Dieu-de-l-elec/Custom-Segmented-Display/CAD and RENDERS/PCB Routing PART4 3.png

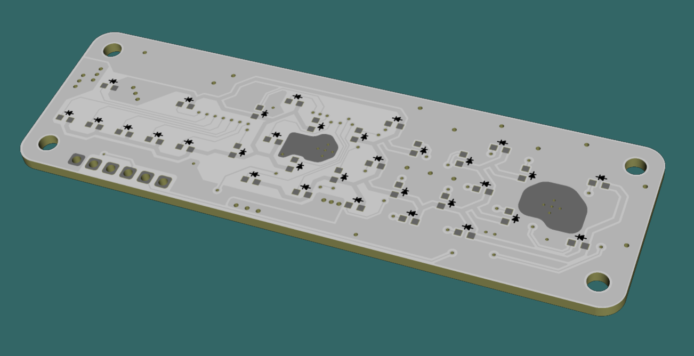
CAD and RENDERS/PCB Routing PART4 3.png
