Dieu-de-l-elec/Custom-Segmented-Display/CAD and RENDERS/PCB Routing PART4 4.png

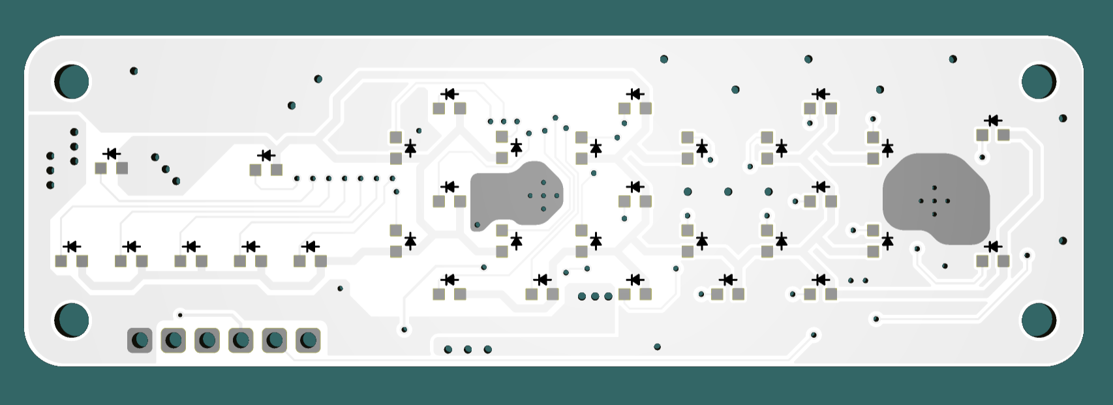
CAD and RENDERS/PCB Routing PART4 4.png
