Dieu-de-l-elec/Custom-Segmented-Display/CAD and RENDERS/PCB Routing PART4 6.png

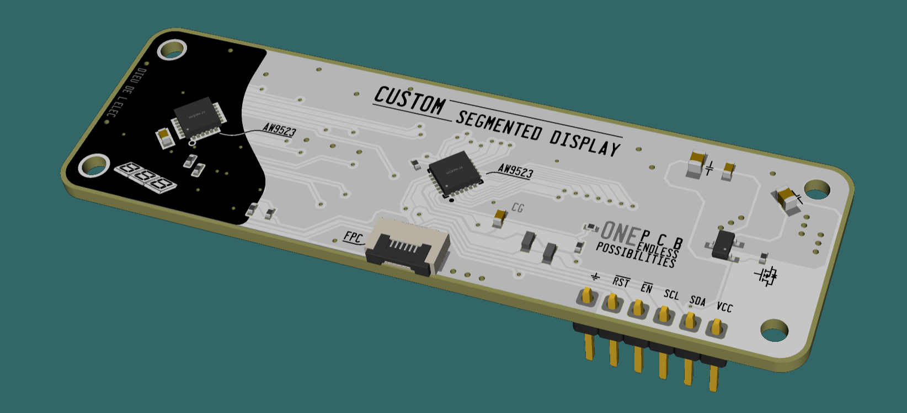
CAD and RENDERS/PCB Routing PART4 6.png
