Dieu-de-l-elec/Custom-Segmented-Display/CAD and RENDERS/RENDER 1.png

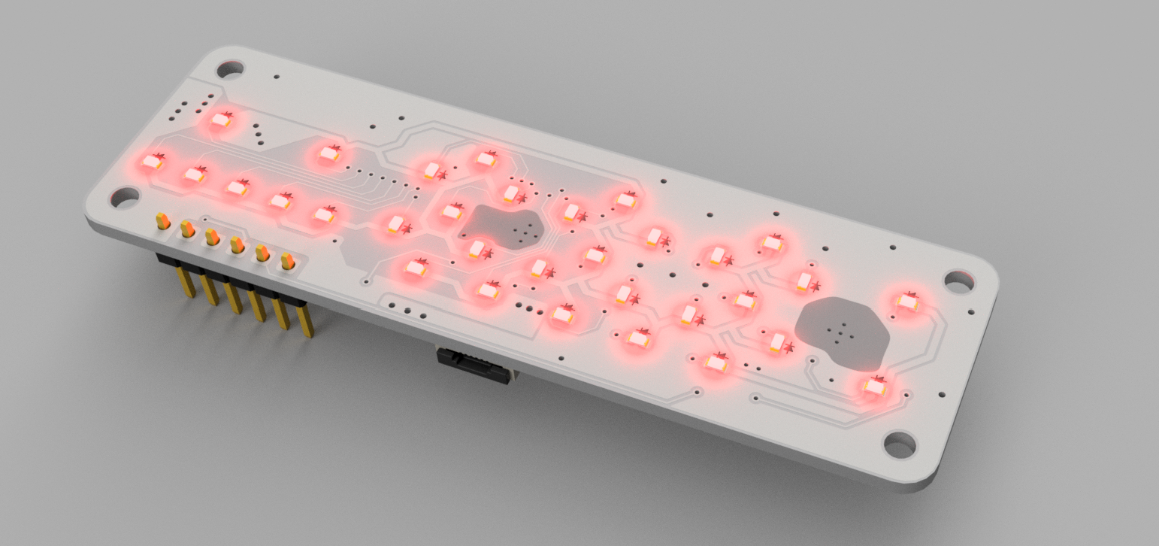
CAD and RENDERS/RENDER 1.png
