Dieu-de-l-elec/Custom-Segmented-Display/CAD and RENDERS/RENDER 1B.png

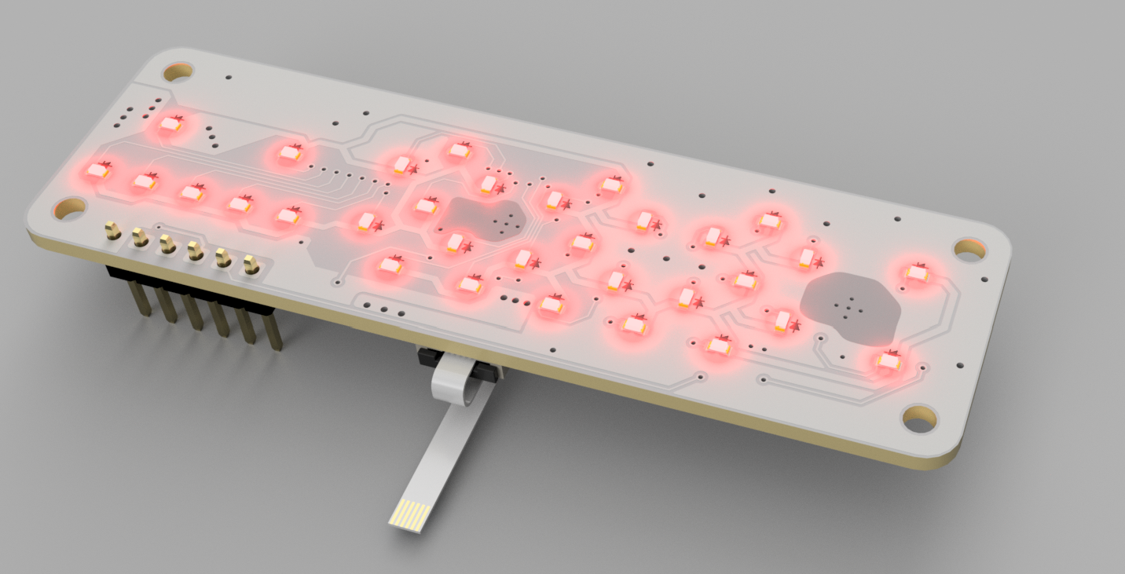
CAD and RENDERS/RENDER 1B.png
