Dieu-de-l-elec/Custom-Segmented-Display/CAD and RENDERS/RENDER 2.png

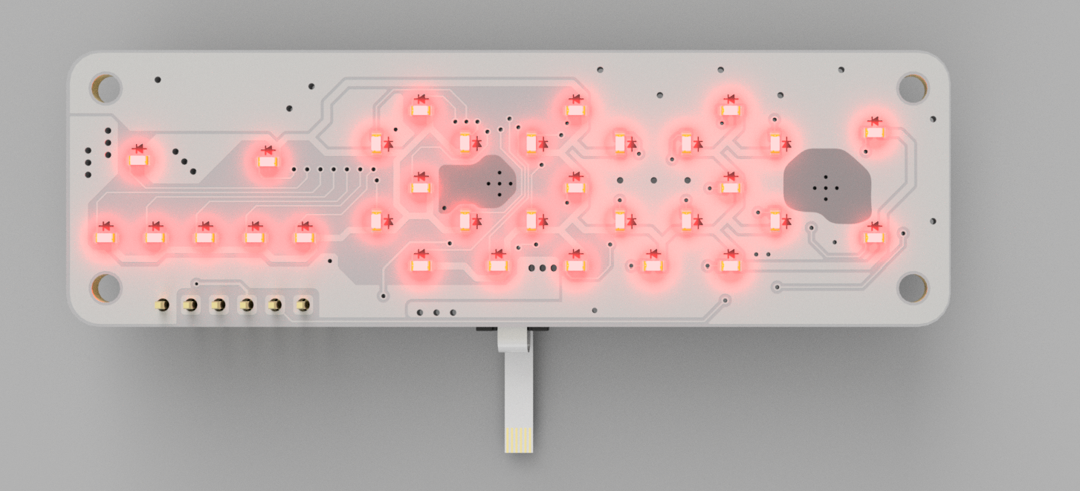
CAD and RENDERS/RENDER 2.png
