Dieu-de-l-elec/Custom-Segmented-Display/CAD and RENDERS/RENDER 3.png

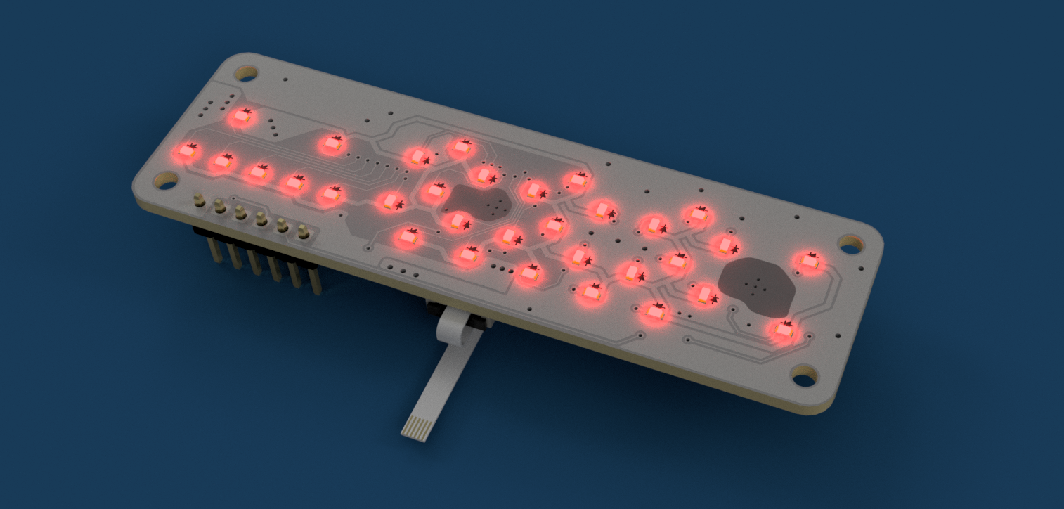
CAD and RENDERS/RENDER 3.png
