Dieu-de-l-elec/Custom-Segmented-Display/CAD and RENDERS/RENDER 4.png

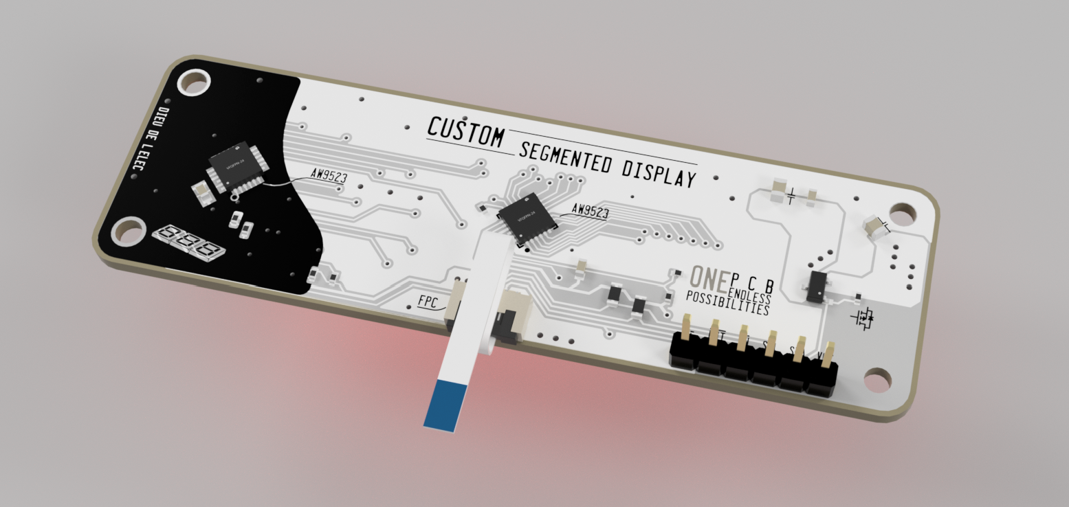
CAD and RENDERS/RENDER 4.png
