Dieu-de-l-elec/Custom-Segmented-Display/CAD and RENDERS/RENDER 5.png

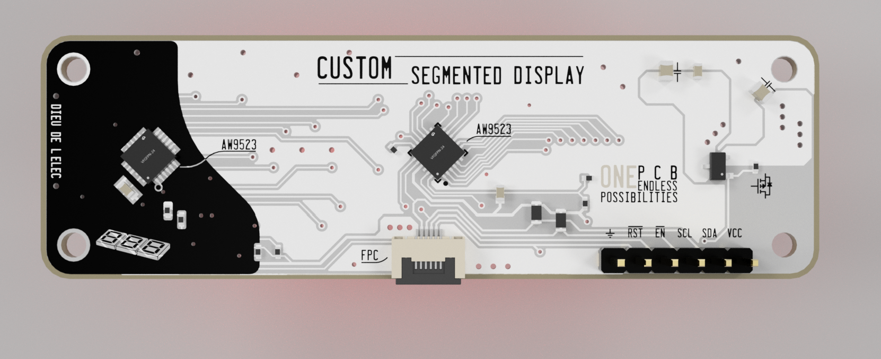
CAD and RENDERS/RENDER 5.png
