Dieu-de-l-elec/Custom-Segmented-Display/CAD and RENDERS/RENDER 6.png

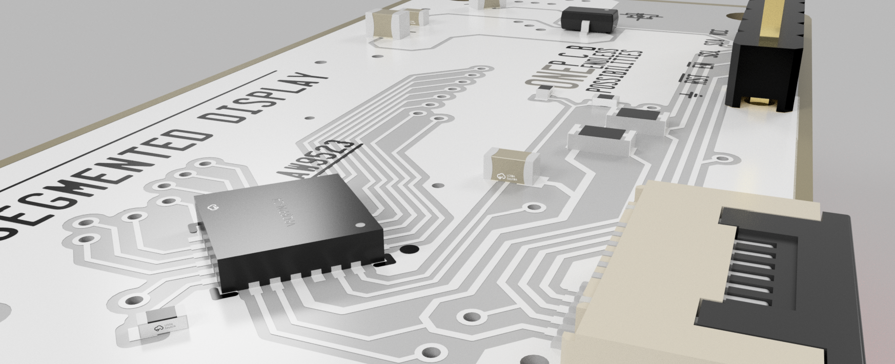
CAD and RENDERS/RENDER 6.png
