Dieu-de-l-elec/Custom-Segmented-Display/CAD and RENDERS/RENDER CAD 1.png

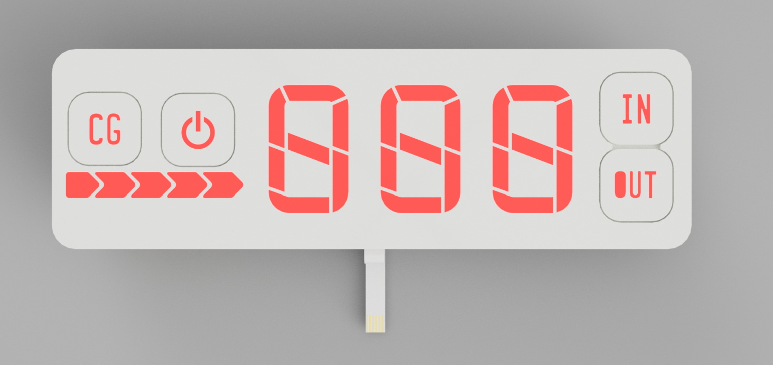
CAD and RENDERS/RENDER CAD 1.png
