Dieu-de-l-elec/Custom-Segmented-Display/CAD and RENDERS/RENDER CAD 2.png

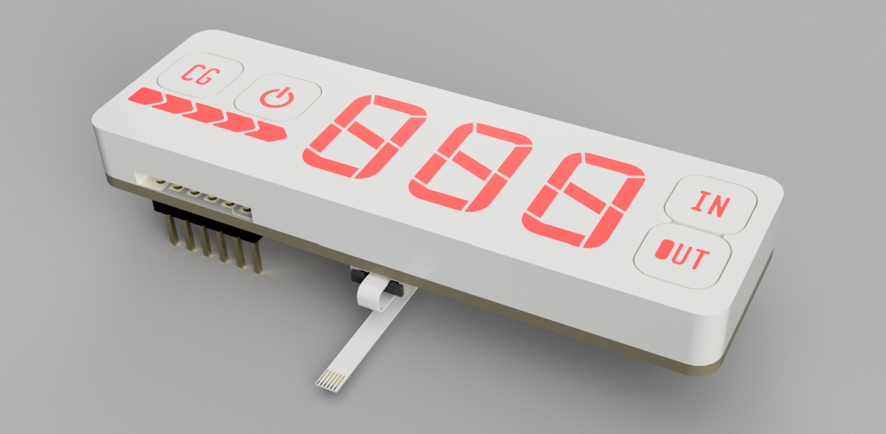
CAD and RENDERS/RENDER CAD 2.png
