Dieu-de-l-elec/Custom-Segmented-Display/CAD and RENDERS/RENDER CAD 3.png

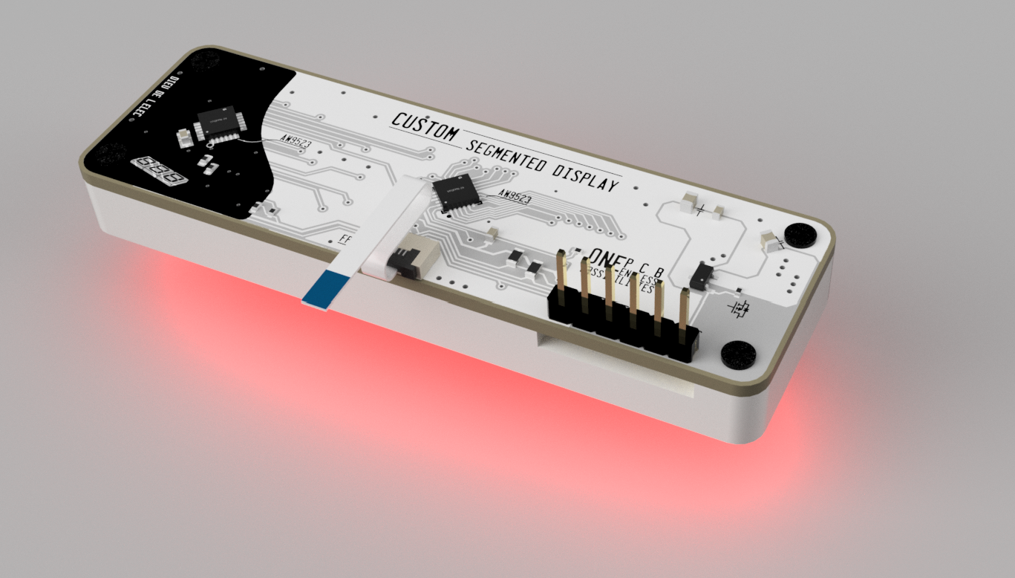
CAD and RENDERS/RENDER CAD 3.png
