Dieu-de-l-elec/Custom-Segmented-Display/CAD and RENDERS/RENDER CAD 5.png

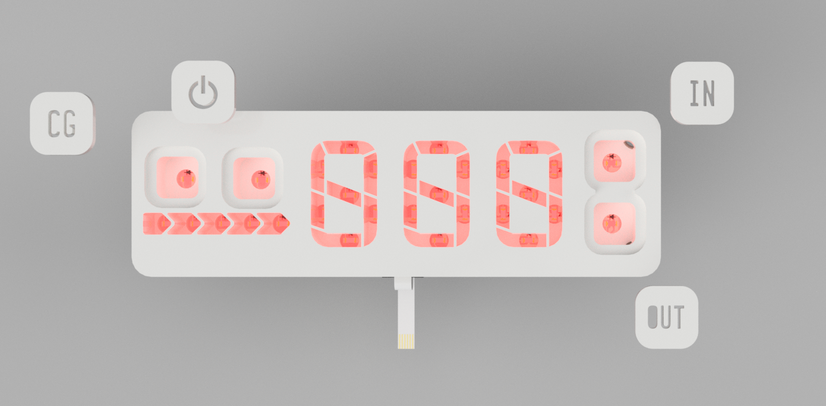
CAD and RENDERS/RENDER CAD 5.png
