Dieu-de-l-elec/Custom-Segmented-Display/CAD and RENDERS/RENDER CAD 7.png

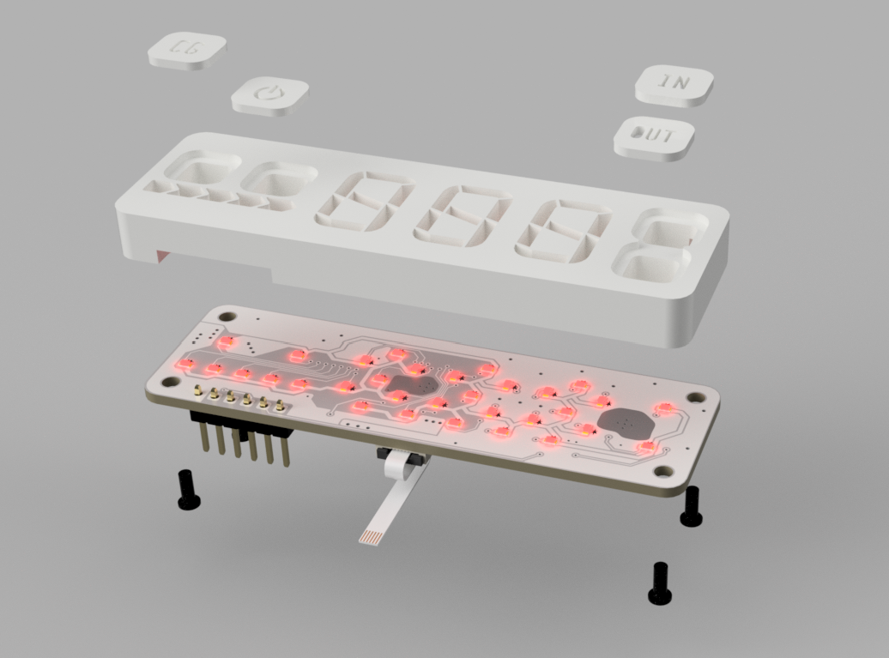
CAD and RENDERS/RENDER CAD 7.png
