Dieu-de-l-elec/Custom-Segmented-Display/Build Imgs/Build 01.jpg

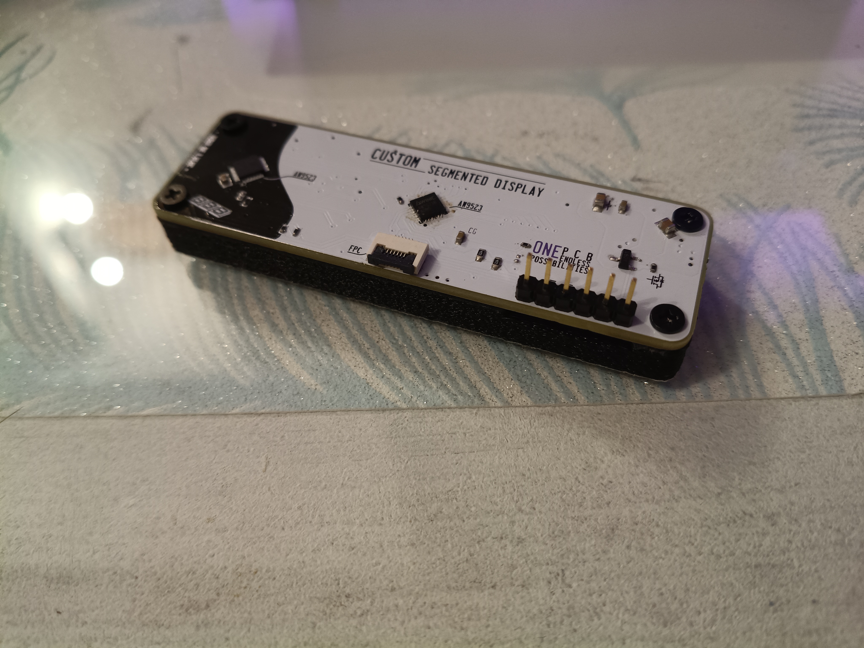
Build Imgs/Build 01.jpg
