Dieu-de-l-elec/Custom-Segmented-Display/Build Imgs/Build 02.jpg

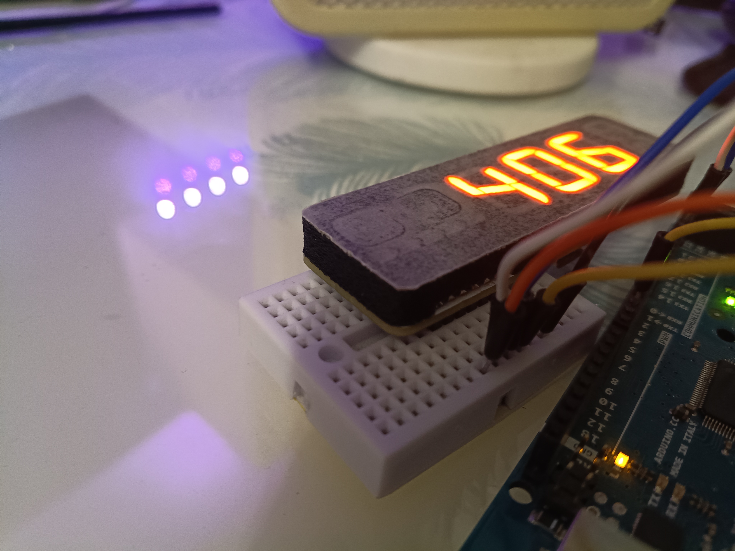
Build Imgs/Build 02.jpg
