Dieu-de-l-elec/Custom-Segmented-Display/Build Imgs/Build 03.jpg

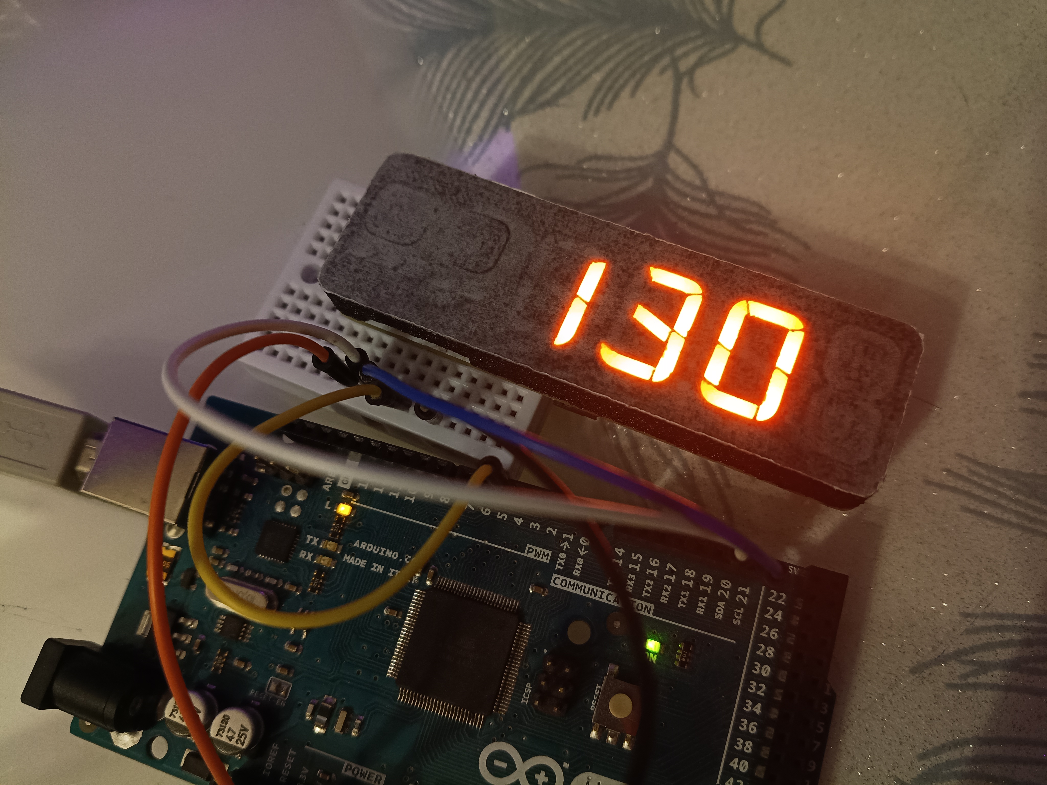
Build Imgs/Build 03.jpg
