Dieu-de-l-elec/Custom-Segmented-Display/Build Imgs/Build 05.jpg

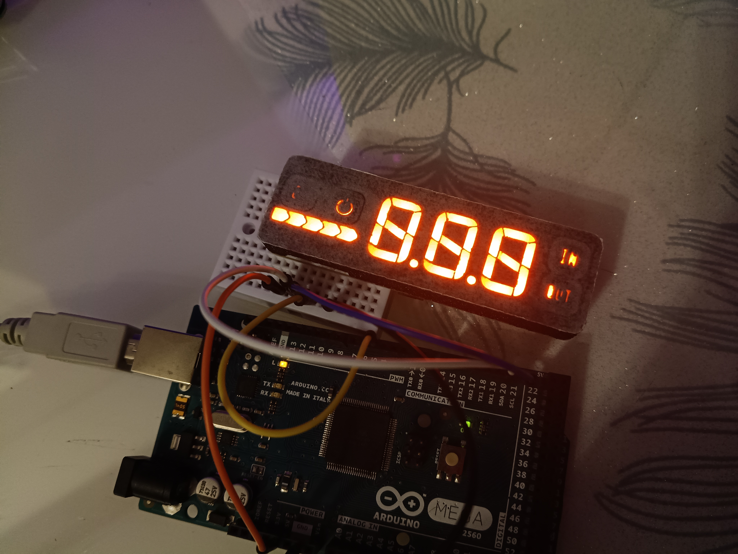
Build Imgs/Build 05.jpg
