Dieu-de-l-elec/Custom-Segmented-Display/Build Imgs/Build 09.jpg

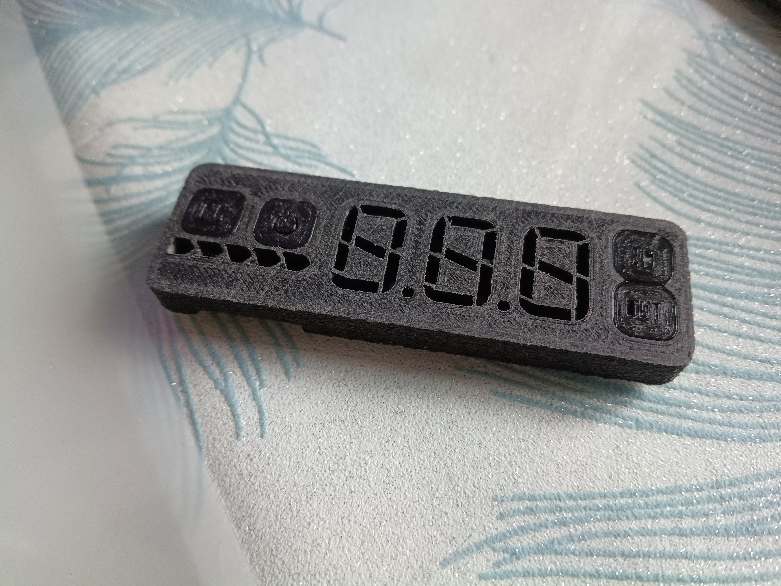
Build Imgs/Build 09.jpg
