Dieu-de-l-elec/Custom-Segmented-Display/Build Imgs/Build 11.jpg

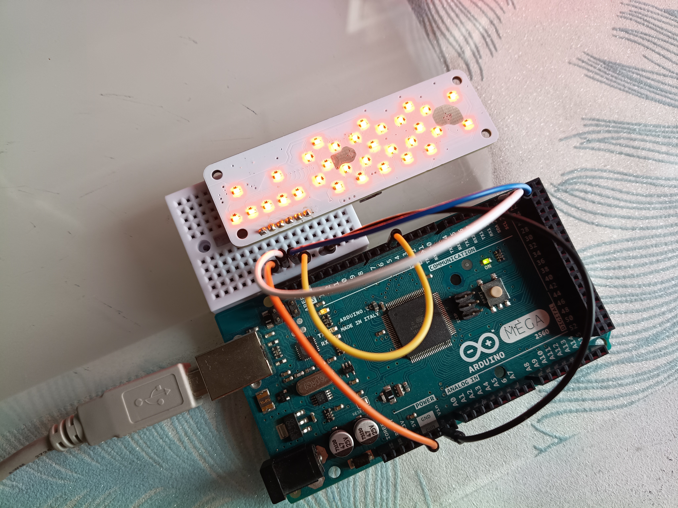
Build Imgs/Build 11.jpg
