Dieu-de-l-elec/Custom-Segmented-Display/Build Imgs/Build 12.jpg

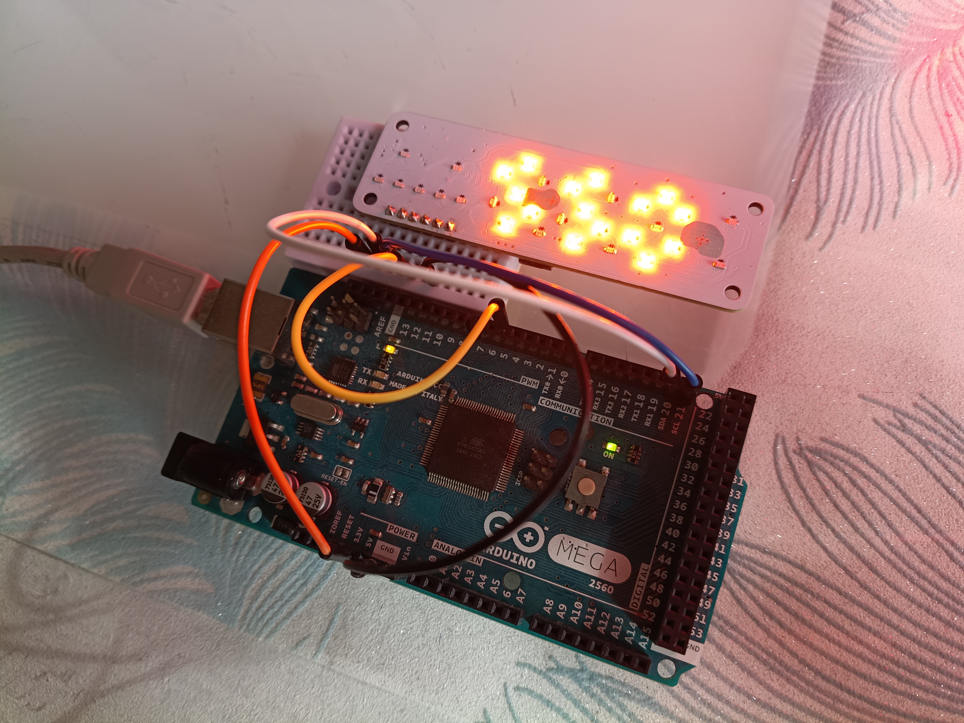
Build Imgs/Build 12.jpg
