Dieu-de-l-elec/Custom-Segmented-Display/Build Imgs/Build 13.jpg

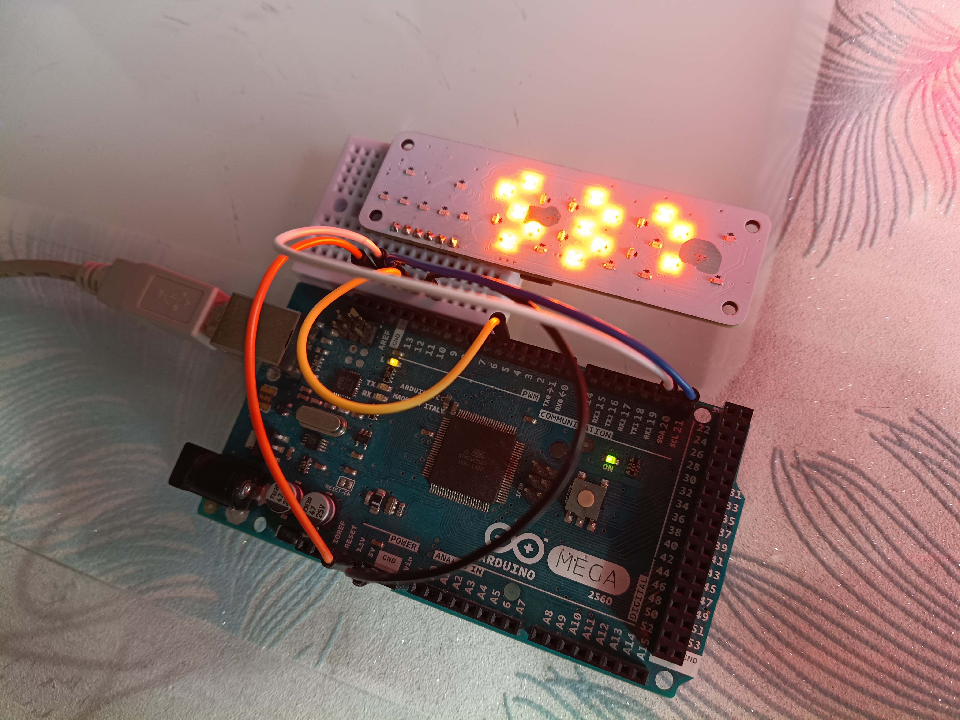
Build Imgs/Build 13.jpg
